franzenhof/lorawan-weather-node/pcblayout/lorawan-weather-node-pcb_Leiterplatte.png

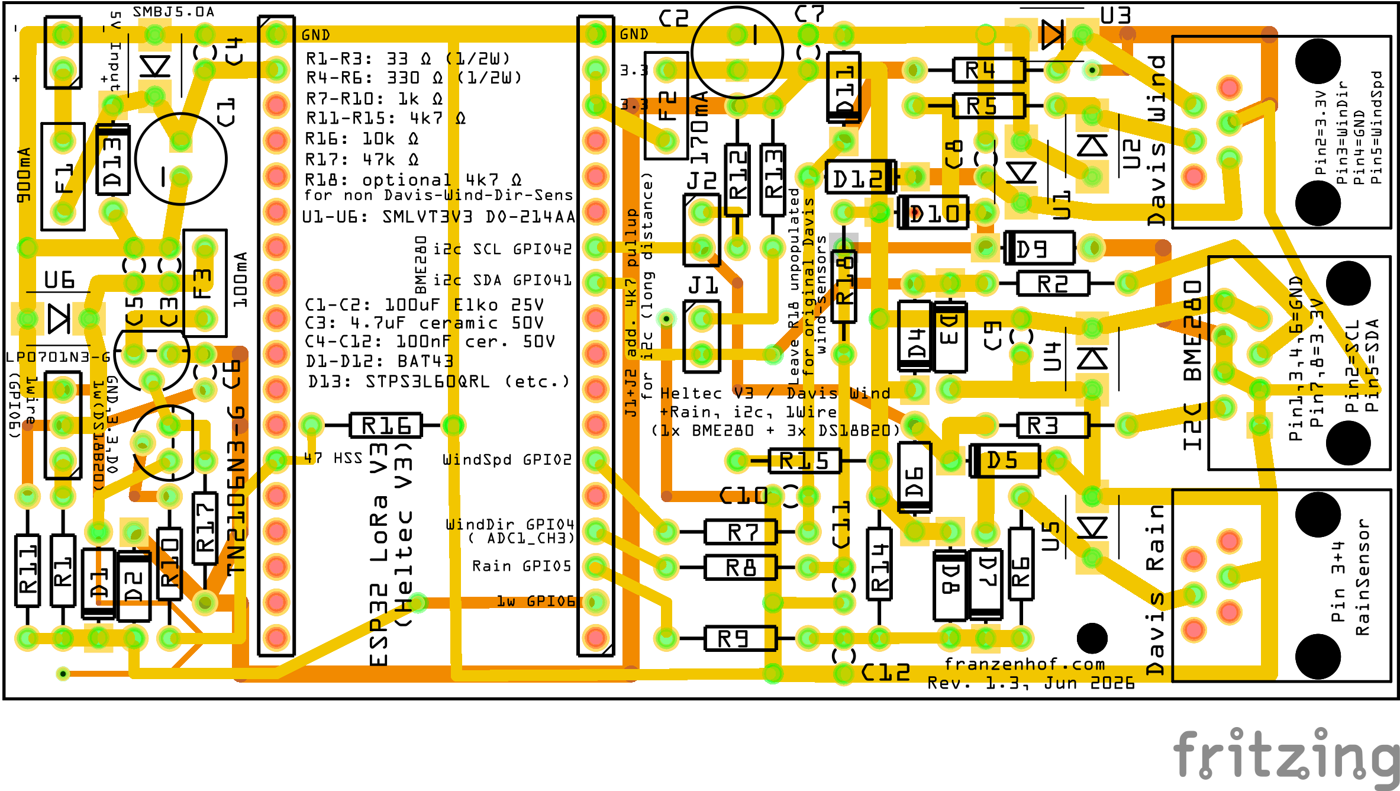
pcblayout/lorawan-weather-node-pcb_Leiterplatte.png
