franzenhof/lorawan-weather-node/pcblayout/lorawan-weather-node-pcb_Schaltplan.png

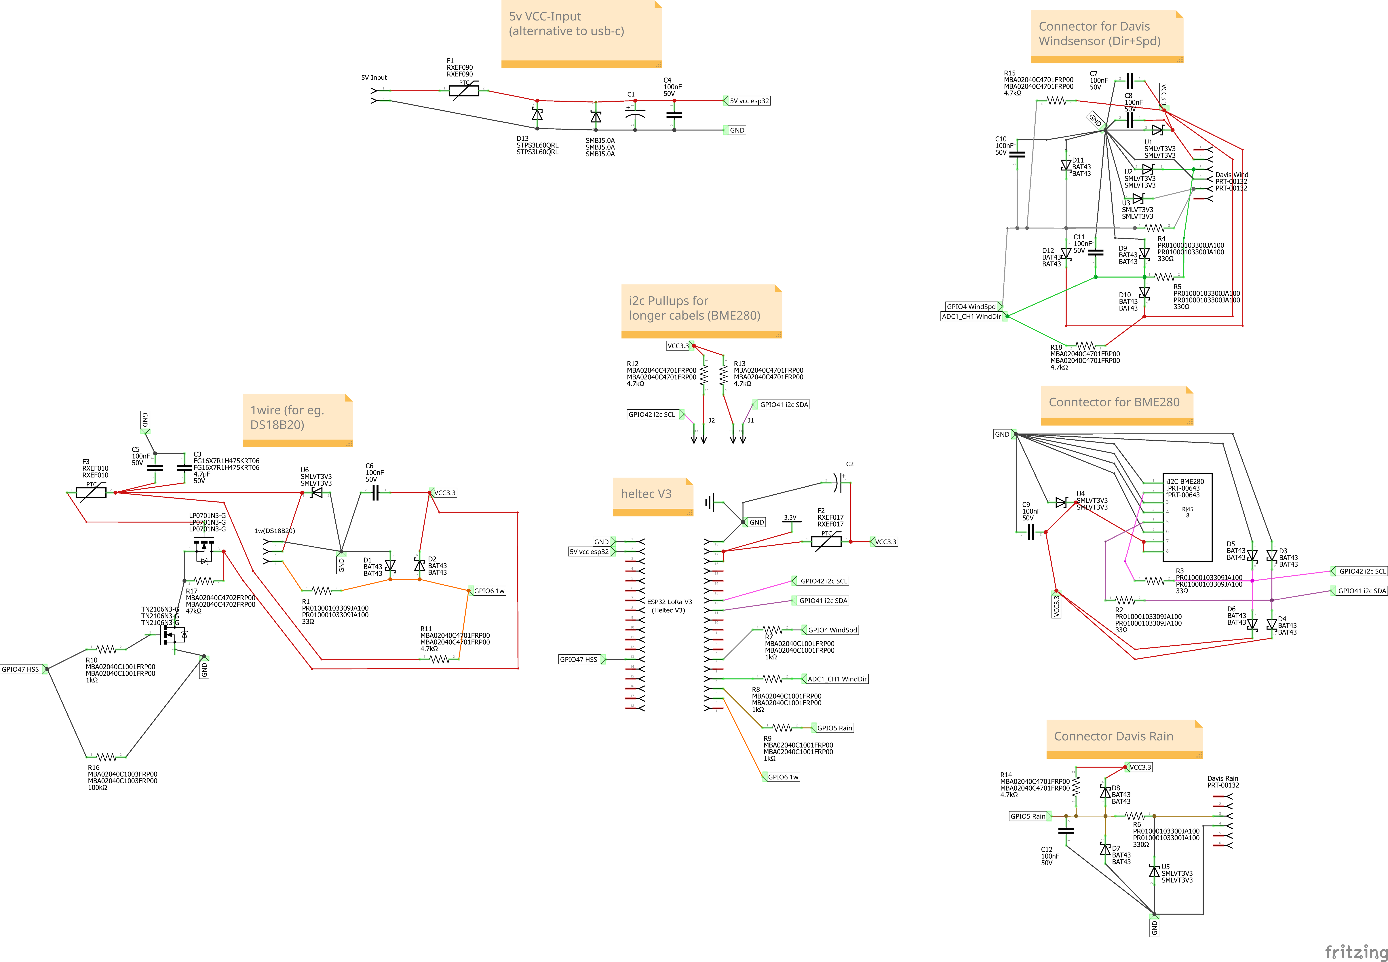
pcblayout/lorawan-weather-node-pcb_Schaltplan.png
