franzenhof/lorawan-weather-node/pictures/wifi-config-generalparameter.png

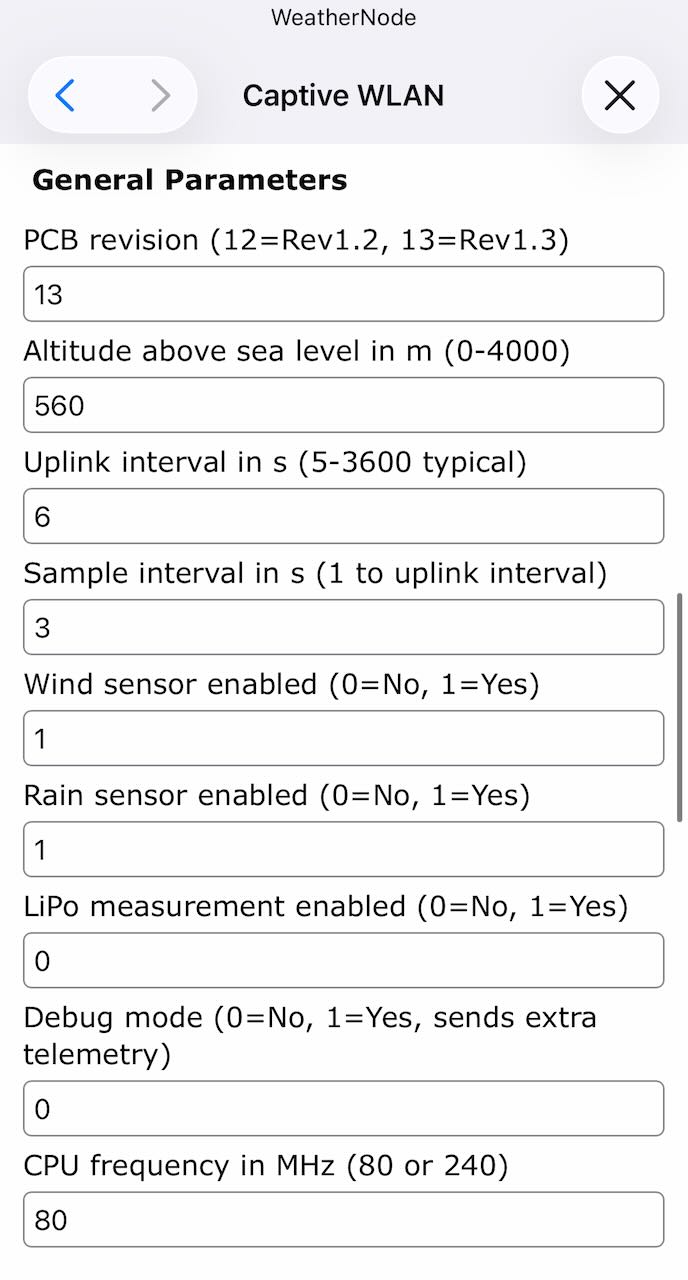
pictures/wifi-config-generalparameter.png
