franzenhof/lorawan-weather-node/pictures/wifi-config-wifimqttparameter.png

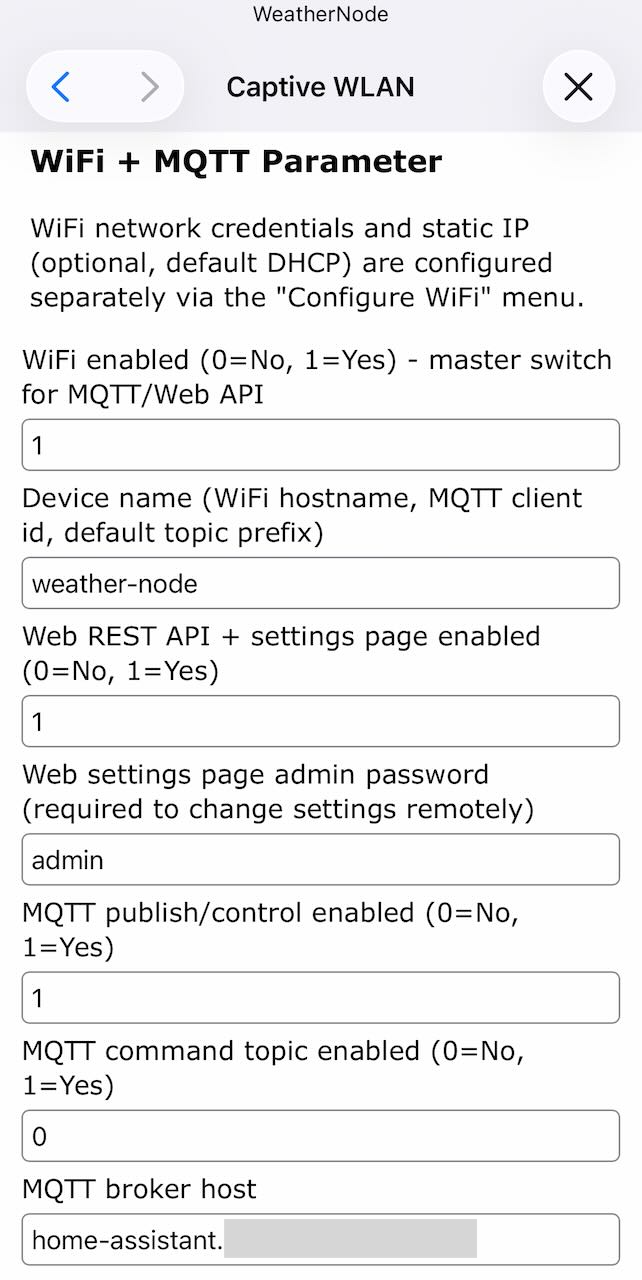
pictures/wifi-config-wifimqttparameter.png
