franzenhof/lorawan-weather-node/src/sensors.h

#pragma once

#include <Arduino.h>

// ============================================================================
// FIXED PIN ASSIGNMENT (independent of PCB revision)
// ============================================================================
#define PIN_ADC_VOLTBATTERY     1   // LiPo voltage measurement (ADC)
#define PIN_ADC_WINDDIRECTION   2   // Davis wind direction (potentiometer, ADC)
#define PIN_ADC_BATCTRL        37   // HIGH enables ADC measurement path (from heltec wifi lora v3 board rev. 3.2)
#define PIN_1WIRE_HSS          47   // High-side switch VCC_1WIRE (LP0701N3-G via VN2222L, from lorawan-weather-node pcb rev 1.3)
#define PIN_I2C_SDA_BME280     41
#define PIN_I2C_SCL_BME280     42

// ============================================================================
// PCNT CONFIGURATION (4k7 pull-up, reed switch to GND, 100 nF low-pass filter)
// ============================================================================
#define PCNT_UNIT_WINDSPEED     PCNT_UNIT_0
#define PCNT_CHANNEL_WINDSPEED  PCNT_CHANNEL_0
#define FILTER_VALUE_WINDSPEED  100   // approx. 1.25 µs at APB=80 MHz → debounce

#define PCNT_UNIT_RAIN          PCNT_UNIT_1
#define PCNT_CHANNEL_RAIN       PCNT_CHANNEL_0
#define FILTER_VALUE_RAIN       100

// ============================================================================
// I2C / BME280
// ============================================================================
#define I2C_FREQUENCY           50000
#define I2C_ADRESS_BME280       0x76

// DS18B20
#define MAX_SENSORS_PER_BUS     3

// ============================================================================
// PIN ASSIGNMENT BY PCB REVISION (runtime)
// Rev 1.2: Wind=GPIO3, Rain=GPIO4, 1-Wire=GPIO5
// Rev 1.3: Wind=GPIO4, Rain=GPIO5, 1-Wire=GPIO6
// ============================================================================
struct PinSet { int windSpeed, rain, oneWire; };
PinSet getPins(int pcbVersion);

// Early ADC pin setup — must run before any possible WiFiManager portal call,
// including the very first boot, so the wind-direction ADC is already usable
// for the portal's "Calibrate Wind Direction" page (see /calibrate/sample in
// portal.cpp). Call once from setup(), before the first-boot portal check.
void sensorsEarlyInit();

// Full sensor init (BME280, 1-Wire, PCNT) — run once gCfg/pcbVersion are
// known, i.e. after the (possible) first-boot portal has completed.
void sensorsInit(const PinSet& pins);

int      adcAverage(int pin, int samples = 8);
float    readBatteryVoltage();
uint16_t readWindDirection();
void     readPulseCounters();   // updates windSpeedMs/windGustMs/rainMM/rainMMSinceStart/rainRateMmH
void     readBme280();          // updates bme280TempC/Humidity/PressAbs/PressSea
// Non-blocking DS18B20 read, split across two calls so loop() (button, WiFi/
// MQTT poll, watchdog) stays responsive during the ~750 ms conversion time
// instead of blocking on it. Call startOneWireConversion() once to kick off
// the read (powers the bus, issues the non-blocking conversion request),
// then pollOneWireConversion() on every following loop() iteration until it
// returns true (conversion complete, bus1Temps[] updated, bus powered back
// down) — only then is it safe to use the DS18B20 values for this cycle.
void     startOneWireConversion();
bool     pollOneWireConversion();

// PCNT control, exposed for params.cpp (wind/rain sensor enable downlink/MQTT params).
void configureWindPcnt();
void stopWindPcnt();
void configureRainPcnt();
void stopRainPcnt();
