franzenhof/lorawan-weather-node/src/lora_payload.h

#pragma once

#include <CayenneLPP.h>
#include <stdint.h>
#include <stddef.h>

// Shared with sendLoRa() (main.cpp), which picks buffer/length/FPort based
// on gCfg.payloadFormat.
extern CayenneLPP lpp;
extern uint8_t    binBuf[64];
extern size_t     binLen;

// Populates `lpp` from the current sensor globals (see globals.h).
void buildLppPacket();

// Populates binBuf/binLen — compact binary alternative to CayenneLPP, see
// chirpstack/decoder.js (parseBin) for the matching decoder.
void buildBinaryPacket();
