franzenhof/lorawan-weather-node/src/serial_log.cpp

#include "serial_log.h"
#include <Arduino.h>

namespace {
constexpr size_t LOG_BUF_SIZE = 8192;
char   logBuf[LOG_BUF_SIZE];
size_t logHead = 0;     // next write position
bool   logFull = false; // true once the buffer has wrapped at least once
}

SerialLog dbgSerial;

size_t SerialLog::write(uint8_t c)
{
    logBuf[logHead] = (char)c;
    logHead = (logHead + 1) % LOG_BUF_SIZE;
    if (logHead == 0) logFull = true;
    return Serial.write(c);
}

size_t SerialLog::write(const uint8_t* buffer, size_t size)
{
    for (size_t i = 0; i < size; i++) {
        logBuf[logHead] = (char)buffer[i];
        logHead = (logHead + 1) % LOG_BUF_SIZE;
        if (logHead == 0) logFull = true;
    }
    return Serial.write(buffer, size);
}

size_t SerialLog::snapshot(char* out, size_t outSize) const
{
    if (outSize == 0) return 0;

    size_t available = logFull ? LOG_BUF_SIZE : logHead;
    size_t start      = logFull ? logHead : 0;        // oldest byte's position
    size_t toCopy      = min(available, outSize - 1);
    size_t skip        = available - toCopy;          // drop oldest bytes if out is smaller than the log

    for (size_t i = 0; i < toCopy; i++) {
        out[i] = logBuf[(start + skip + i) % LOG_BUF_SIZE];
    }
    out[toCopy] = '\0';
    return toCopy;
}

void SerialLog::clear()
{
    logHead = 0;
    logFull = false;
}
